arzaman/smartPID/Code/HWTest/SmartPID_logo_1bit.c

unsigned char SmartPID_128x39_1bit_horiz [] = {
0x00, 0x00, 0x04, 0x00, 0x00, 0x00, 0x00, 0x00, 0x00, 0x00, 0x00, 0x00, 0x00, 0x00, 0x00, 0x00,
0x00, 0x00, 0x06, 0x00, 0x00, 0x00, 0x00, 0x00, 0x00, 0x00, 0x00, 0x00, 0x00, 0x00, 0x00, 0x00,
0x00, 0x00, 0x0A, 0x08, 0x00, 0x00, 0x00, 0x00, 0x00, 0x00, 0x00, 0x00, 0x00, 0x00, 0x00, 0x00,
0x00, 0x00, 0x0B, 0x08, 0x00, 0x00, 0x00, 0x00, 0x00, 0x00, 0x00, 0x00, 0x00, 0x00, 0x00, 0x00,
0x00, 0x00, 0x09, 0x14, 0x20, 0x00, 0x00, 0x00, 0x00, 0x00, 0x00, 0x00, 0x00, 0x00, 0x00, 0x00,
0x00, 0x00, 0x09, 0x14, 0x20, 0x40, 0x00, 0x00, 0x00, 0x00, 0x00, 0x00, 0x00, 0x00, 0x00, 0x00,
0x00, 0x00, 0x09, 0x14, 0x50, 0xC0, 0x00, 0x00, 0x00, 0x00, 0x00, 0x00, 0x00, 0x00, 0x00, 0x00,
0x00, 0x00, 0x09, 0x14, 0xD1, 0x23, 0x80, 0x00, 0x00, 0x00, 0x00, 0x00, 0x00, 0x00, 0x00, 0x00,
0x00, 0x00, 0x09, 0x16, 0x99, 0x24, 0x40, 0x00, 0x00, 0x00, 0x00, 0x00, 0x00, 0x00, 0x00, 0x00,
0x00, 0x00, 0x09, 0xB2, 0x89, 0x18, 0x3F, 0xFF, 0xFF, 0xFF, 0xFF, 0xFF, 0xFF, 0xFF, 0xFF, 0xE0,
0x00, 0x00, 0x08, 0xA2, 0x89, 0x00, 0x00, 0x00, 0x00, 0x00, 0x00, 0x00, 0x00, 0x00, 0x00, 0x18,
0x0F, 0xFE, 0x08, 0xA2, 0x89, 0x00, 0x00, 0x00, 0x00, 0x00, 0x7F, 0xFF, 0x06, 0x3F, 0xFF, 0x84,
0x1F, 0xFE, 0x08, 0xA3, 0x86, 0x00, 0x00, 0x00, 0x00, 0x00, 0x7F, 0xFF, 0x86, 0x3F, 0xFF, 0xE4,
0x38, 0x00, 0x08, 0xE1, 0x04, 0x00, 0x00, 0x00, 0x00, 0x60, 0x60, 0x01, 0xC6, 0x30, 0x00, 0xF2,
0x70, 0x00, 0x08, 0x41, 0x00, 0x00, 0x00, 0x00, 0x00, 0x60, 0x60, 0x00, 0xC6, 0x30, 0x00, 0x32,
0x60, 0x00, 0x08, 0x40, 0x00, 0x00, 0x00, 0x00, 0x00, 0x60, 0x60, 0x00, 0xC6, 0x30, 0x00, 0x3A,
0x60, 0x00, 0x08, 0x00, 0x00, 0x00, 0x00, 0x00, 0x00, 0x60, 0x60, 0x00, 0xC6, 0x30, 0x00, 0x1A,
0x70, 0x00, 0x08, 0x7E, 0x1F, 0x80, 0xFF, 0xC1, 0xBD, 0xFE, 0x60, 0x00, 0xC6, 0x30, 0x00, 0x1A,
0x38, 0x00, 0x0A, 0xFF, 0x3F, 0xC0, 0xFF, 0xE1, 0xFD, 0xFE, 0x60, 0x01, 0xC6, 0x30, 0x00, 0x1A,
0x1F, 0xFF, 0x8B, 0xC3, 0xF0, 0xE0, 0x00, 0x71, 0xE0, 0x60, 0x6F, 0xFF, 0x86, 0x30, 0x00, 0x1A,
0x0F, 0xFF, 0xCB, 0x81, 0xE0, 0x60, 0x00, 0x31, 0xC0, 0x60, 0x6F, 0xFF, 0x06, 0x30, 0x00, 0x1A,
0x00, 0x00, 0xEB, 0x00, 0xC0, 0x60, 0x00, 0x31, 0x80, 0x60, 0x60, 0x00, 0x06, 0x30, 0x00, 0x1A,
0x00, 0x00, 0x6B, 0x00, 0xC0, 0x61, 0xFF, 0xF1, 0x80, 0x60, 0x60, 0x00, 0x06, 0x30, 0x00, 0x1A,
0x00, 0x00, 0x6B, 0x00, 0xC0, 0x63, 0xFF, 0xF1, 0x80, 0x60, 0x60, 0x00, 0x06, 0x30, 0x00, 0x1A,
0x00, 0x00, 0x6B, 0x00, 0xC0, 0x67, 0x00, 0x31, 0x80, 0x60, 0x60, 0x00, 0x06, 0x30, 0x00, 0x3A,
0x00, 0x00, 0x6B, 0x00, 0xC0, 0x66, 0x00, 0x31, 0x80, 0x60, 0x60, 0x00, 0x06, 0x30, 0x00, 0x32,
0x00, 0x01, 0xEB, 0x00, 0xC0, 0x67, 0x01, 0xF1, 0x80, 0x60, 0x60, 0x00, 0x06, 0x30, 0x00, 0xF2,
0x7F, 0xFF, 0xCB, 0x00, 0xC0, 0x63, 0xFF, 0xF1, 0x80, 0x60, 0x60, 0x00, 0x06, 0x3F, 0xFF, 0xE2,
0x7F, 0xFF, 0x0B, 0x00, 0xC0, 0x61, 0xFF, 0x31, 0x80, 0x60, 0x60, 0x00, 0x06, 0x3F, 0xFF, 0x82,
0x00, 0x00, 0x08, 0x00, 0x00, 0x00, 0x00, 0x00, 0x00, 0x00, 0x00, 0x00, 0x00, 0x00, 0x00, 0x02,
0x00, 0x00, 0x08, 0x00, 0x00, 0x00, 0x00, 0x00, 0x00, 0x00, 0x00, 0x00, 0x00, 0x00, 0x00, 0x02,
0x00, 0x00, 0x08, 0x78, 0x78, 0x44, 0x7C, 0x78, 0x78, 0x40, 0x81, 0xF3, 0xC0, 0x01, 0x00, 0x02,
0x00, 0x00, 0x08, 0x80, 0x84, 0x64, 0x10, 0x44, 0x84, 0x40, 0x81, 0x02, 0x20, 0x02, 0x80, 0x02,
0x00, 0x00, 0x10, 0x80, 0x84, 0x54, 0x10, 0x44, 0x84, 0x40, 0x81, 0x02, 0x20, 0x04, 0x40, 0x04,
0x00, 0x3F, 0xE0, 0x80, 0x84, 0x54, 0x10, 0x78, 0x84, 0x40, 0x81, 0xF3, 0xC7, 0xF8, 0x43, 0xF8,
0x00, 0x00, 0x00, 0x80, 0x84, 0x54, 0x10, 0x50, 0x84, 0x40, 0x81, 0x02, 0x80, 0x00, 0x44, 0x00,
0x00, 0x00, 0x00, 0x80, 0x84, 0x4C, 0x10, 0x48, 0x84, 0x40, 0x81, 0x02, 0x40, 0x00, 0x28, 0x00,
0x00, 0x00, 0x00, 0x78, 0x78, 0x44, 0x10, 0x44, 0x78, 0x7C, 0xF9, 0xF2, 0x20, 0x00, 0x28, 0x00,
0x00, 0x00, 0x00, 0x00, 0x00, 0x00, 0x00, 0x00, 0x00, 0x00, 0x00, 0x00, 0x00, 0x00, 0x10, 0x00
};
