arzaman/smartPID/Code/HWTest/delay.h

/*
  Copyright (c) 2015 Arduino LLC.  All right reserved.

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
  You should have received a copy of the GNU Lesser General Public
  License along with this library; if not, write to the Free Software
  Foundation, Inc., 51 Franklin St, Fifth Floor, Boston, MA  02110-1301  USA
*/

#ifndef _DELAY_
#define _DELAY_

#include <stdint.h>
#include "variant.h"

#ifdef __cplusplus
extern "C" {
#endif

/**
 * \brief Returns the number of milliseconds since the Arduino board began running the current program.
 *
 * This number will overflow (go back to zero), after approximately 50 days.
 *
 * \return Number of milliseconds since the program started (uint32_t)
 */
extern uint32_t millis( void ) ;

/**
 * \brief Returns the number of microseconds since the Arduino board began running the current program.
 *
 * This number will overflow (go back to zero), after approximately 70 minutes. On 16 MHz Arduino boards
 * (e.g. Duemilanove and Nano), this function has a resolution of four microseconds (i.e. the value returned is
 * always a multiple of four). On 8 MHz Arduino boards (e.g. the LilyPad), this function has a resolution
 * of eight microseconds.
 *
 * \note There are 1,000 microseconds in a millisecond and 1,000,000 microseconds in a second.
 */
extern uint32_t micros( void ) ;

/**
 * \brief Pauses the program for the amount of time (in miliseconds) specified as parameter.
 * (There are 1000 milliseconds in a second.)
 *
 * \param dwMs the number of milliseconds to pause (uint32_t)
 */
extern void delay( uint32_t dwMs ) ;

/**
 * \brief Pauses the program for the amount of time (in microseconds) specified as parameter.
 *
 * \param dwUs the number of microseconds to pause (uint32_t)
 */
#if defined(__ICCARM__)
static __inline__ void delayMicroseconds( uint32_t );
#else
static __inline__ void delayMicroseconds( uint32_t ) __attribute__((always_inline, unused)) ;
#endif
static __inline__ void delayMicroseconds( uint32_t usec )
{
  if ( usec == 0 )
  {
    return ;
  }

  /*
   *  The following loop:
   *
   *    for (; ul; ul--) {
   *      __asm__ volatile("");
   *    }
   *
   *  produce the following assembly code:
   *
   *    loop:
   *      subs r3, #1        // 1 Core cycle
   *      bne.n loop         // 1 Core cycle + 1 if branch is taken
   */

  // VARIANT_MCK / 1000000 == cycles needed to delay 1uS
  //                     3 == cycles used in a loop
  uint32_t n = usec * (VARIANT_MCK / 1000000) / 3;
#if defined(__ICCARM__)
//  n/=3;
  n--;
__asm volatile( "MOV R0, %0\n\t" ::"r"(n));
__asm volatile //("mov r0, (n) \n"
  ("loop: subs r0, #1 \n"
  " bhi loop \n");
#else
#ifndef _Windows
  __asm__ __volatile__(
	"1:              \n"
	"   sub %0, #1   \n" // substract 1 from %0 (n)
	"   bne 1b       \n" // if result is not 0 jump to 1
	: "+r" (n)           // '%0' is n variable with RW constraints
	:                    // no input
	:                    // no clobber
  );
#endif
#endif
  // https://gcc.gnu.org/onlinedocs/gcc/Extended-Asm.html
  // https://gcc.gnu.org/onlinedocs/gcc/Extended-Asm.html#Volatile
}

#ifdef __cplusplus
}
#endif

#endif /* _DELAY_ */
